YttrisL/maimai-dx-conversion-guide/docs/etape-1-pc-alls.md

# 🛠️ Étape 1 : Le Remplacement du PC Central (ALLS)

L'ancien PC *Ringedge 2* n'est pas assez puissant pour faire tourner *DX*. Vous avez besoin d'un PC **ALLS HX2**.
Alternativement, il est souvent plus simple (et moins cher) de trouver des PC **ALLS MX2**, et ceux-ci peuvent être modifiés (downgrade) pour correspondre exactement aux spécifications d'un HX2.

* **Stockage :** Le HX2 vient de base avec un SSD de 128 Go et un disque dur de 512 Go. Pour une installation sur serveur privé, ces disques suffisent.
* **Alimentation (Attention) :** L'alimentation interne du *Ringedge 2* fournissait directement les tensions nécessaires à différents composants de la borne *Finale*. Le connecteur molex en façade du *Ringedge 2* fournit au reste de la borne du 12v, du 5v et du 3,3v. Le nouveau PC *ALLS* ne possède pas ces connecteurs d'alimentation similaire. **La solution idéale** est d'ajouter une petite alimentation secondaire (arcade PSU) distincte de celle du PC *ALLS* pour alimenter les PCBs et les lumières. Une alimentation 12v/5v sera suffisante, aucun composant de la borne *Finale* n'exploite le 3,3v.

---

Passons à l'[Étape 2 : Affichage et dalles tactiles ADX](etape-2-affichage-tactile.md).
