YttrisL/maimai-dx-conversion-guide/docs/en/equipment-checklist.md

---
title: "☑️ Purchase checklist"
---

# ☑️ Purchase checklist

*Need details on where to buy, why, and alternatives? See the [full shopping list](equipment.md).*

## Mandatory hardware

- [ ] ALLS HX2
- [ ] Sega IO4 I/O board
- [ ] Aime reader (Gen. 3)
- [ ] **2x**{: .quantity-emphasis } HDX touchscreen
- [ ] **16x**{: .quantity-emphasis } HDX buttons
- [ ] **2x**{: .quantity-emphasis } OBSF-24TR button
- [ ] **1x**{: .quantity-emphasis } 4-port USB hub
- [ ] **1x**{: .quantity-emphasis } 5V/12V switching power supply

## Optional hardware (camera and QR-code)

- [ ] **1x**{: .quantity-emphasis } Player camera
- [ ] **2x**{: .quantity-emphasis } QR-code camera

## Small supplies

### Cables

- [ ] **1x**{: .quantity-emphasis } HDMI to DVI-D cable (3 m)
- [ ] **1x**{: .quantity-emphasis } DVI-D to DVI-D cable (2 m)
- [ ] **1x**{: .quantity-emphasis } DB-9 Female-Female cable
- [ ] **4x**{: .quantity-emphasis } DB-9 Male-Female cable (3 m)
- [ ] **1x**{: .quantity-emphasis } IEC C-13 cable (2 m)
- [ ] **2x**{: .quantity-emphasis } micro-USB cable
- [ ] **2x**{: .quantity-emphasis } 3.5 mm male-to-male jack cable

### Electronics

- [ ] **2x**{: .quantity-emphasis } TTL to RS-232 converter with female DB-9
- [ ] **2x**{: .quantity-emphasis } Raspberry Pi Pico
- [ ] **2x**{: .quantity-emphasis } Pico-2CH-RS232
- [ ] **2x**{: .quantity-emphasis } Headphone audio amplifier
- [ ] **2x**{: .quantity-emphasis } 3.5 mm female jack socket

### Hookup wire

- [ ] Flexible hookup wire (AWG 20), ideally in several colors

### Lighting (optional cameras)

- [ ] **1x**{: .quantity-emphasis } 12V warm white LED strip
- [ ] **1x**{: .quantity-emphasis } 12V common-anode RGB LED strip (about 20 cm)
- [ ] **1x**{: .quantity-emphasis } 12V red LED (with built-in resistor)

### Connectors

- [ ] **1x**{: .quantity-emphasis } Molex Mini-Fit Jr. 2x7-pin female connector
- [ ] **30x**{: .quantity-emphasis } Molex Mini-Fit Jr. female crimp pin
- [ ] **1x**{: .quantity-emphasis } JST-RA 2x10-pin female connector
- [ ] **30x**{: .quantity-emphasis } JST-RA female crimp pin
- [ ] **2x**{: .quantity-emphasis } JST-SM 8-pin female connector
- [ ] **2x**{: .quantity-emphasis } JST-SM 2-pin connector (male + female pair)
- [ ] JST-XH connector kit
- [ ] JST-PH connector kit

!!! abstract "Work in progress"
    More small supplies will be added to this checklist as they are detailed on the [full shopping list](equipment.md#small-supplies).
