YttrisL/maimai-dx-conversion-guide/docs/fr/equipment-checklist.md

---
title: "☑️ Checklist d'achat"
---

# ☑️ Checklist d'achat

*Besoin de détails sur où acheter, pourquoi, et des alternatives ? Consultez la [liste de courses complète](equipment.md).*

## Matériel obligatoire

- [ ] ALLS HX2
- [ ] Carte I/O Sega IO4
- [ ] Lecteur Aime (Gen. 3)
- [ ] **2x**{: .quantity-emphasis } Dalle tactile HDX
- [ ] **16x**{: .quantity-emphasis } Boutons HDX
- [ ] **2x**{: .quantity-emphasis } Bouton OBSF-24TR
- [ ] **1x**{: .quantity-emphasis } Hub USB 4 ports
- [ ] **1x**{: .quantity-emphasis } Alimentation à découpage 5V/12V

## Matériel optionnel (caméra et QR-code)

- [ ] **1x**{: .quantity-emphasis } Caméra des joueurs
- [ ] **2x**{: .quantity-emphasis } Caméra pour QR-Code

## Petites fournitures

### Câbles

- [ ] **1x**{: .quantity-emphasis } Câble HDMI vers DVI-D (3 m)
- [ ] **1x**{: .quantity-emphasis } Câble DVI-D vers DVI-D (2 m)
- [ ] **1x**{: .quantity-emphasis } Câble DB-9 Femelle-Femelle
- [ ] **4x**{: .quantity-emphasis } Câble DB-9 Mâle-Femelle (3 m)
- [ ] **1x**{: .quantity-emphasis } Câble IEC C-13 (2 m)
- [ ] **2x**{: .quantity-emphasis } Câble micro-USB
- [ ] **2x**{: .quantity-emphasis } Câble jack 3.5 mm mâle-mâle

### Électronique

- [ ] **2x**{: .quantity-emphasis } Convertisseur TTL vers RS-232 avec DB-9 femelle
- [ ] **2x**{: .quantity-emphasis } Raspberry Pi Pico
- [ ] **2x**{: .quantity-emphasis } Pico-2CH-RS232
- [ ] **2x**{: .quantity-emphasis } Ampli audio pour casque
- [ ] **2x**{: .quantity-emphasis } Prise jack 3.5 mm femelle

### Fils de câblage

- [ ] Fil de câblage souple (AWG 20), idéalement de plusieurs couleurs

### Éclairage (caméras optionnelles)

- [ ] **1x**{: .quantity-emphasis } Bande de LEDs blanc chaud 12V
- [ ] **1x**{: .quantity-emphasis } Bande de LEDs RGB 12V à anode commune (environ 20 cm)
- [ ] **1x**{: .quantity-emphasis } LED rouge 12V (avec résistance intégrée)

### Connecteurs

- [ ] **1x**{: .quantity-emphasis } Connecteur Molex Mini-Fit Jr. 2x7 broches femelle
- [ ] **30x**{: .quantity-emphasis } Broche Molex Mini-Fit Jr. femelle à sertir
- [ ] **1x**{: .quantity-emphasis } Connecteur JST-RA 2x10 broches femelle
- [ ] **30x**{: .quantity-emphasis } Broche JST-RA femelle à sertir
- [ ] **2x**{: .quantity-emphasis } Connecteur JST-SM 8 broches femelle
- [ ] **2x**{: .quantity-emphasis } Connecteur JST-SM 2 broches (paire mâle + femelle)
- [ ] Kit de connecteurs JST-XH
- [ ] Kit de connecteurs JST-PH

!!! abstract "En cours d'écriture"
    D'autres petites fournitures viendront s'ajouter à cette checklist au fur et à mesure qu'elles seront détaillées sur la [liste de courses complète](equipment.md#petites-fournitures).
