YttrisL/maimai-dx-conversion-guide/docs/fr/spiralglide-resources.md

---
title: "Les ressources de SpiralGlide"
---

# 🖨️ Les ressources de SpiralGlide

L'inspiration de base de ce guide est basé sur le travail de **SpiralGlide**, un membre de la communauté qui a documenté sa propre conversion *FiNALE → DX* et conçu plusieurs pièces imprimables en 3D pour l'opération. Cette page rassemble ces ressources d'origine.

## Les notes de conversion originales

* **[Notes de conversion DxNALE (PDF)](../resources/pdfs/dxnale-original-guide.pdf)** : le document de référence original rédigé par SpiralGlide, qui a servi de base à ce guide.

## Les pièces imprimables en 3D

SpiralGlide a modélisé les supports permettant de monter le lecteur Aime et le lecteur de QR code de DX de façon non-destructrice sur la tour centrale de la borne. Cela représente quatre fichiers `.stl`, répartis en deux ensembles.

### Support du lecteur Aime

Un seul bloc à imprimer, sur lequel s'installe le lecteur Aime de Star Horse 4 et qui vient prendre sa place dans la façade de la tour centrale dans les trous de vis prévus pour maintenir l'acrylique.

* **[maimai-aime-reader.stl](../resources/models/spiralglide/maimai-aime-reader.stl)** : support du lecteur Aime.
* **[maimai-aime-reader.ipt](../resources/models/spiralglide/maimai-aime-reader.ipt)** : fichier source Autodesk Inventor du support.

!!! lightbox
    Le support du lecteur Aime imprimé et monté dans la façade de la tour centrale, lecteur Aime en place. Photo par SpiralGlide

### Support du lecteur de QR code (DX Pass Reader)

Trois pièces qui s'empilent : le boîtier qui se loge dans la tour centrale, la plaque intermédiaire qui positionne la caméra (carte face arrière vers l'extérieur, code vers le bas), et la façade percée de deux ouvertures.

* **[dxnale-dx-pass-reader.stl](../resources/models/spiralglide/dxnale-dx-pass-reader.stl)** : boîtier principal.
* **[dxnale-dx-pass-reader-midpanel-v2.stl](../resources/models/spiralglide/dxnale-dx-pass-reader-midpanel-v2.stl)** : plaque intermédiaire.
* **[dxnale-dx-pass-reader-front-panel-v2.stl](../resources/models/spiralglide/dxnale-dx-pass-reader-front-panel-v2.stl)** : façade.

!!! lightbox
    Vue éclatée du support du lecteur de QR code : le boîtier, la plaque intermédiaire à deux ouvertures, et la façade « DX PASS READER »

---
