YttrisL/maimai-dx-conversion-guide/docs/etape-4-lecteur-aime.md

# 💳 Étape 4 : Le Lecteur de Cartes Aime

Les anciens lecteurs de cartes de la *Finale* sont obsolètes et ne fonctionneront pas avec *DX*.

1. Vous devez vous procurer un lecteur Aime moderne (Génération 3, numéro de pièce : **610-0955**).
2. Installez-le sur le panneau central de la borne, de préférence via une impression 3D pour réaliser une installation non-destructrice.
3. **Bonne nouvelle :** L'ordre des fils (pinout) sur le connecteur est presque identique à l'ancien modèle. Vous pouvez réutiliser les câbles de communication de l'ancien lecteur sans avoir à tout recâbler.
4. **Adresses et Branchement :**
   * Le lecteur Aime doit être branché au port **COM1**.
   * Le petit écran texte (VFD) doit être raccordé au port **COM2**.
   * Vous pouvez récupérer du courant 5V sur les anciens câbles pour alimenter ces deux éléments.

**Sur le PC *ALLS HX* :** Le port matériel correspondant au COM1 est la prise série située à gauche des ports USB et de la prise réseau. *([Manuel](pdfs/maimai-dx-manual-full.pdf), page 128)*.

---

Passons à l'[Étape 5 : Compatibilité avec le système d'origine via le Proxy](etape-5-proxy-compatibilite.md).
