YttrisL/maimai-dx-conversion-guide/docs/etape-6-son-casques.md

# 🎧 Étape 6 : Prises casques et Système Son

La borne *DX* propose des prises casques pour les joueurs, ce qui n'existait pas sur *Finale*.

L'ordinateur *ALLS HX* possède 4 sorties audio classiques (type Jack). Trois sont situées sur la carte mère principale, et une sur une carte d'extension *([Manuel](pdfs/maimai-dx-manual-full.pdf), page 128)*.
**Attention :** L'ordinateur ne sort qu'un son "pré-amplifié" (très faible). Dans une vraie borne *DX*, ce son passe par un gros amplificateur dédié. Vous pouvez réutiliser l'amplificateur de la *Finale* pour les haut-parleurs principaux, mais il ne gérera pas les nouvelles prises casques.

Voici à quoi correspondent les ports audio de l'ordinateur : *(Voir [manuel](pdfs/maimai-dx-manual-full.pdf), page 193)*

* **FRONT :** Sortie pour les haut-parleurs du Joueur 1
* **REAR :** Sortie pour les haut-parleurs du Joueur 2
* **C/W :** Sortie pour la prise casque du Joueur 1
* **SIDE :** Sortie pour la prise casque du Joueur 2

## Comment installer les prises casques

Puisque le signal pour les casques (sorties C/W et SIDE) est trop faible, vous devez acheter un ou deux petits amplificateurs audio bon marché. **Inutile d'acheter des amplis avec des molettes de volume :** le volume des casques se règle numériquement directement dans les menus du jeu *DX*.

Pour l'installation physique des prises (qui sont de simples connecteurs Jack 3.5mm femelles), vous avez deux options :

1. **La méthode fidèle :** Percer la coque en plastique sous les boutons (comme sur une vraie *DX*) pour y encastrer les prises.
2. **La méthode non-destructrice :** Installer les deux prises casque au centre de la borne, entre les deux joueurs, via un boîtier réalisé manuellement.

**Astuce :** En salle d'arcade, les prises jack s'abîment très vite à force de brancher/débrancher les écouteurs. Prévoyez un système où la prise fixée sur la coque est facilement remplaçable (par exemple, reliez-la à l'amplificateur interne avec un câble détachable, plutôt que de souder le connecteur directement sur l'ampli).

---

Étape suivante (optionnelle) : les [Lumières](etape-7-lumieres.md).
