YttrisL/maimai-dx-conversion-guide/docs/lexique.md

# 📖 Petit Lexique pour les Débutants

Pour ne pas être perdu dans les termes techniques :

* **ALLS (MX2 / HX2) :** C'est le nom de l'ordinateur standard utilisé par Sega pour faire tourner les jeux récents. Il remplace l'ancien PC de Finale (nommé Ringedge 2).
* **Carte I/O (Input/Output) :** C'est la carte électronique qui fait le lien entre le PC et la borne. Elle capte l'appui sur les boutons. Dans le cas de *maimai Finale*, il s'agit d'une **Sega IO3**. Pour *DX*, elle doit être remplacée par une **Sega IO4**.
* **Ports COM (COM1, COM3...) :** Ce sont les "adresses" (ou canaux) virtuelles par lesquelles le PC communique avec certains périphériques spécifiques (comme les dalles tactiles ou le lecteur de carte *Aime*). Aujourd'hui, la plupart des connexions sur Port COM se font via des ports virtuels, toutefois un ALLS HX2 dispose de quatre connexions physiques pour y connecter le matériel de la borne.
* **Aime / VFD :** Le lecteur de cartes sans contact (NFC) utilisé par les joueurs pour sauvegarder leur profil. Le *VFD* (Vacuum Fluorescent Display) est le petit écran à affichage rétro (souvent vert ou bleu) qui affiche le solde d'argent ou d'autres informations textuelles.

---

Le vocabulaire est clair ? Passons à la [Liste de courses](materiel.md).
