YttrisL/maimai-dx-conversion-guide/docs/materiel.md

# 🛒 Liste de courses : Le matériel nécessaire

Avant de commencer, voici la liste des composants à acquérir pour réaliser cette conversion :

## Matériel Obligatoire

* Un PC ALLS HX2 (ou un MX2 modifié).
* Une carte I/O Sega IO4.
* Deux dalles tactiles ADX.
* Un lecteur Aime de 3ème génération (référence de la pièce : 610-0955).
* Un câble DisplayPort (ou DisplayPort vers DVI) et un câble DVI-D pour les écrans.
* Deux petits amplificateurs audio pour gérer les prises casques.

## Pour le Proxy ("Traduction" des données)

* Deux Raspberry Pi 5 avec leur bloc d'alimentation.
* Deux adaptateurs "USB-to-Serial" avec puces FTDI (prévoyez-en 6 si vous gérez le tactile **et** les LEDs via proxy).
* Deux adaptateurs "Null Modem" pour faire correspondre les fiches mâle-femelle des adaptateurs "USB-to-Serial" à la connectique du ALLS.

## Matériel Optionnel (Son, Caméras, Finitions)

* Une webcam classique et bon marché pour la caméra du joueur.
* Deux webcams au format strict UVC 640x480 pour les lecteurs de QR-Code.
* Un Hub USB (de préférence avec sa propre alimentation).

---

Consultez ensuite les [avertissements](avertissements.md) avant de vous lancer.
