YttrisL/maimai-dx-conversion-guide/docs/en/warnings.md

---
title: "⚠️ Warnings"
---

# ⚠️ Warnings and Considerations

Before you dive in, here is the reality of the project:

* **It is practically irreversible.** We avoid destructive modifications as much as possible, but most of the FiNALE cabinet's core components will be replaced with DX-compatible hardware. Going back to *FiNALE* remains possible in theory if you keep all the original parts, but it would be a fresh conversion, just as tedious.
* **It is expensive.** Budget **around 2000 to 2500 EUR** for the parts. Most of the hardware is only available second-hand, on Japanese resale sites or from private sellers who set their own prices. The total therefore varies with the period and availability.
* **It takes time.** Do not expect to start in the morning and be done by the evening. Even with every part and tool on hand, plan for **several days** of work. *If you are an operator*, keep in mind that the cabinet will be out of service until the conversion is complete.
* **Test beforehand.** Make sure your *FiNALE* cabinet works perfectly before you start, since several of its components will be reused. **Fix any power, sound, LED or screen problem first.** The buttons, touchscreens, Aime readers, camera, I/O board and RingEdge 2, on the other hand, will be replaced: a fault on one of them is therefore minor.

The task is complex, but this guide presents every point in a simple and detailed way, explaining the concepts you need at each step.

Also keep in mind that, even though the goal is the most faithful DX experience possible, **this cabinet will remain a conversion**. Gameplay does not suffer from it, but some details specific to a real DX can never be reproduced on a FiNALE base.

!!! tip "Before you dive in"
    Most components will come from Asia, often with long delivery times. To avoid an out-of-service cabinet for several months, **get every component before starting the conversion**, and **check that they work**. The next page details the purchases to plan.

If, knowing these warnings, you are still determined to go ahead, let's move on to the rest of the guide.

---

Not a technical expert? Feel free to consult the [glossary](glossary.md) before moving on to the [shopping list](equipment.md).
