YttrisL/maimai-dx-conversion-guide/docs/fr/index.md

---
title: "Accueil"
---

# Guide Complet : Projet "DxNALE"

## Convertir une borne FiNALE en DX

Bienvenue dans ce guide détaillé pour **convertir une borne d'arcade FiNALE en DX**. Il s'appuie sur [les ressources de SpiralGlide](spiralglide-resources.md), enrichies pour rester accessibles *même si vous n'êtes pas ingénieur en électronique*.

---

## Qu'est-ce que "DxNALE" ?

DxNALE est le nom donné par la communauté aux bornes FiNALE converties pour faire tourner DX. Les deux systèmes sont radicalement différents : **DX ne peut pas tourner sur une borne FiNALE d'origine.**

Une rumeur tenace veut que la conversion soit un travail titanesque, presque irréalisable. **Il n'en est rien.** Certaines étapes sont effectivement complexes, mais ce guide vous accompagne tout au long de l'opération.

!!! tip "L'objectif : une fidélité logicielle parfaite"
    Il serait possible de modifier les données du jeu pour le rendre compatible avec n'importe quelle modification matérielle. Ce guide vise au contraire une fidélité logicielle totale.

    **Aucune modification logicielle du jeu n'est tolérée.** Le jeu doit "penser" qu'il tourne sur une borne d'origine : toute notre adaptation matérielle doit donc lui être invisible.

    Avantage : la borne obtenue est en théorie compatible avec la philosophie de la plupart des grands serveurs privés pour DX.

---

## Par où commencer ?

1. Lisez les **[Avertissements](warnings.md)** pour comprendre les enjeux et les conséquences de la conversion.
2. Consultez la **[Liste de courses](equipment.md)** : vous aurez besoin de chacun des éléments mentionnés.
3. Suivez les **étapes dans l'ordre**, en commençant par l'[Étape 1 : PC Central (ALLS)](step-1-alls-and-psu.md).

Un terme vous semble obscur ? Le [Lexique](glossary.md) regroupe toutes les définitions utiles aux débutants.

Les protocoles série sont au cœur de cette conversion. Si vous ne les maîtrisez pas, l'annexe "[Comprendre les protocoles série](understanding-serial-protocols.md)" les explique en partant de zéro.

**Félicitations d'avance !** En suivant toutes ces étapes, vous obtiendrez une borne *DxNALE* 100 % fonctionnelle et prête pour le jeu en ligne.

---

Prêt à vous lancer ? Commençons par les [Avertissements](warnings.md).
