YttrisL/maimai-dx-conversion-guide/docs/fr/secondhand-market.md

---
title: "Le marché de l'occasion"
---

# 📦 À propos du marché de l'occasion japonais

## Introduction

*Hormis les petites fournitures*, la plupart des composants de cette conversion **ne se trouvent pas dans le commerce**. C'est du matériel d'arcade très spécifique, vendu uniquement par les fabricants officiels, et passer par le service après-vente de Sega est évidemment impossible. Il ne reste donc que la vente entre particuliers.

**Nous dépendons donc de ce qui est disponible sur le marché de l'occasion.** Une carte Sega IO4 ou un lecteur Aime se trouvent assez facilement, un ALLS HX2 beaucoup moins, et une dalle tactile officielle de DX est pour ainsi dire introuvable. Pour certaines pièces, des alternatives existent. Pour les autres, il faudra prendre votre mal en patience et guetter une offre sur le marché de l'occasion japonais.

!!! tip "D'où viennent les pièces détachées ?"
    La plupart des pièces d'occasion japonaises proviennent de bornes démantelées pour être revendues plus facilement, le plus souvent après la fermeture d'une salle d'arcade ou parce que la borne n'attirait plus de joueurs. DX étant très populaire, ses bornes sont rarement exportées, et encore plus rarement démontées pour être vendues en pièces détachées.

    Heureusement, **la plupart des composants Sega sont interchangeables** et réutilisés d'une borne à l'autre, y compris sur des machines bien moins populaires que DX, dont on trouve beaucoup plus facilement les pièces.

## Acheter via un proxy

La plupart des pièces de la [liste de courses](equipment.md) se trouvent sur **JDirectItems Auction**, le plus grand site d'enchères du Japon. Problème : comme la grande majorité des sites de vente japonais, il exige **une adresse, un numéro de téléphone et un moyen de paiement japonais**. Sans résider au Japon, impossible donc d'y acheter directement.

C'est là qu'interviennent les **services de proxy d'achat** : des entreprises disposant d'une adresse et d'un compte au Japon, qui enchérissent, achètent et réceptionnent les colis en votre nom, puis vous les réexpédient à l'international. Ils facturent une commission et des frais de service, en plus du prix de l'article et des frais d'envoi.

Parmi ces services :

* **[Neokyo]({{NEOKYO}})**
* **[Zenmarket]({{ZENMARKET}})**
* **[FROM JAPAN]({{FROM_JAPAN}})**
* **[Buyee]({{BUYEE}})** : l'un des plus connus et des plus anciens, mais lisez l'avertissement ci-dessous.

!!! warning "Buyee n'expédie pas certaines pièces électroniques"
    Buyee refuse d'expédier à l'international tout article contenant une pile ou une batterie au lithium, en application des réglementations sur le transport aérien de matières dangereuses. Or, certaines pièces recherchées, comme le ALLS HX2, embarquent une petite pile bouton au lithium qui alimente leur horloge interne (RTC) hors tension. **Dans les faits, ces pièces ne peuvent donc pas être expédiées via Buyee.**

    Pour ces articles, préférez un service comme Neokyo ou Zenmarket, qui n'appliquent pas cette restriction.

Le fonctionnement est similaire d'un service à l'autre :

1. Vous créez un compte.
2. Vous soumettez le lien de l'article qui vous intéresse (ou parcourez JDirectItems Auction directement depuis leur site).
3. Vous créditez votre compte du montant nécessaire, et le proxy se charge de l'achat.
4. Le proxy reçoit l'article et le stocke pour vous.
    * La plupart des services stockent gratuitement les articles pendant une certaine durée.
    * Vous pouvez ainsi **regrouper plusieurs articles** dans leur entrepôt pour tout expédier en un seul colis.
5. Une fois prêt, demandez le conditionnement : le proxy emballe vos articles et les expédie à votre adresse hors du Japon.

!!! tip "Demandez des photos avant l'envoi"
    Une fois l'article arrivé dans leur entrepôt, vous pouvez généralement demander **des photos supplémentaires** avant de valider l'envoi. C'est très utile pour vérifier l'état d'une pièce d'occasion avant qu'elle ne traverse la moitié du globe. Vous ne serez pas remboursé en cas de problème, mais vous saurez tout de suite s'il faut chercher la pièce ailleurs, sans attendre de recevoir le colis.

## Astuces pour la recherche

Trouver la bonne pièce sur JDirectItems Auction peut être frustrant sans quelques bases :

* **Cherchez avec les références officielles.** Une recherche en anglais ou en français ne donne presque jamais de résultats pertinents. Utilisez plutôt les noms et références des schémas et manuels officiels (par exemple `ALLS HX2`, `IO4`, `Aime`), qui restent les mêmes en japonais puisqu'il s'agit de références commerciales. Un traducteur (DeepL, Google Traduction) vous aidera à comprendre le titre et la description d'une annonce.
* **Ne fuyez pas la mention « ジャンク » (*junk*).** Du matériel fonctionnel est souvent vendu ainsi, simplement parce qu'il n'a pas été testé récemment. Ce n'est pas forcément cassé : c'est juste vendu « en l'état », sans garantie.
* **Vérifiez le vendeur.** Le pourcentage d'évaluations positives (en haut à droite de l'annonce) est un bon indicateur de fiabilité. Un vendeur professionnel habitué à démonter des bornes d'arcade est généralement un gage de sérieux.
* **Examinez les photos.** Les vendeurs japonais sont généralement très rigoureux sur les photos, même sans description en anglais. Zoomez sur les connecteurs, l'état des broches et les étiquettes ou marquages qui confirment la référence exacte de la pièce.
* **Surveillez l'heure de fin d'enchère.** Les enchères se terminent à l'heure japonaise (JST, UTC+9), souvent en pleine nuit en France. La plupart des proxys permettent de placer à l'avance une **enchère automatique maximale** : inutile de rester éveillé pour surenchérir à la dernière seconde.
* **Anticipez les frais annexes.** Le prix affiché n'est jamais le prix final. Ajoutez :
    * la commission du proxy ;
    * le transport jusqu'à son entrepôt ;
    * l'envoi international, souvent calculé au poids **et** au volume ;
    * les éventuels frais de douane à la réception, qui varient selon votre pays.

    Une carte électronique compacte reste généralement raisonnable à expédier, mais gardez ce calcul en tête avant d'enchérir trop haut sur une pièce rare.
* **Créez une alerte.** La plupart des proxys permettent d'enregistrer une recherche et d'être notifié dès qu'un nouvel article correspondant apparaît. C'est particulièrement utile pour les pièces rares comme le ALLS HX2, qui peuvent mettre des semaines, voire des mois, à réapparaître.
