YttrisL/maimai-dx-conversion-guide/docs/fr/warnings.md

---
title: "⚠️ Avertissements"
---

# ⚠️ Avertissements et Considérations

Avant de vous lancer, voici la réalité du projet :

* **C'est pratiquement irréversible.** Nous évitons autant que possible les modifications destructives, mais la plupart des éléments centraux de la borne FiNALE vont être remplacés par du matériel compatible DX. Revenir à *FiNALE* reste théoriquement possible si vous conservez toutes les pièces d'origine, mais ce serait une nouvelle conversion, tout aussi fastidieuse.
* **C'est coûteux.** Comptez **environ 2000 à 2500 €** de pièces. La plupart du matériel ne se trouve que d'occasion, sur les sites de revente japonais ou auprès de particuliers qui fixent librement leurs prix. Ce montant varie donc selon la période et la disponibilité.
* **C'est long.** N'espérez pas commencer le matin et terminer le soir. Même avec toutes les pièces et tout le matériel en main, comptez **plusieurs jours** de travail. *Si vous êtes exploitant*, gardez en tête que la borne restera hors service jusqu'à la fin de la conversion.
* **Testez avant.** Vérifiez que votre borne *FiNALE* fonctionne parfaitement avant de commencer, car plusieurs de ses composants seront réutilisés. **Réglez d'abord tout problème d'alimentation, de son, de LEDs ou d'écrans.** À l'inverse, les boutons, les dalles tactiles, les lecteurs Aime, la caméra, la carte I/O et le RingEdge 2 seront remplacés : un défaut sur l'un d'eux est donc mineur.

La tâche est complexe, mais ce guide présente chaque point de façon simple et détaillée, en expliquant à chaque étape les notions nécessaires.

Gardez aussi en tête que, même si l'objectif est une expérience DX la plus fidèle possible, **cette borne restera une conversion**. L'expérience de jeu n'en souffre pas, mais certains détails propres à une véritable DX ne pourront jamais être reproduits sur une base FiNALE.

!!! tip "Avant de vous lancer"
    La plupart des composants viendront d'Asie, avec des délais de livraison souvent longs. Pour éviter une borne hors service pendant plusieurs mois, **procurez-vous tous les composants avant de commencer la conversion**, et **vérifiez qu'ils fonctionnent**. La page suivante détaille les achats à prévoir.

Si, en connaissance de ces avertissements, vous êtes toujours décidé à vous lancer, passons à la suite du guide.

---

Vous n'êtes pas un expert technique ? N'hésitez pas à consulter le [lexique](glossary.md) avant de passer à la [liste de courses](equipment.md).
