YttrisL/maimai-dx-conversion-guide/docs/fr/conclusion.md

---
title: "Conclusion"
---

# 🎉 Conclusion

**Félicitations !** Si vous avez suivi toutes ces étapes, vous possédez désormais une borne *maimai DxNALE* fonctionnelle et prête pour le jeu en ligne !

---

## Pour aller plus loin

Le guide est terminé, mais quelques annexes restent à portée de main si besoin :

* **[Manuels officiels](official-manuals.md)** - Les manuels de maintenance d'origine (*maimai DX* et *maimai PiNK*), pour retrouver une référence précise ou une procédure constructeur.
* **[Schémas de câblage](wiring-diagrams.md)** - Les planches de câblage extraites de ces manuels en haute résolution, pour retrouver un fil sans avoir à zoomer dans un PDF de plusieurs dizaines de Mo.
* **[Comprendre les protocoles série](understanding-serial-protocols.md)** - Un petit cours pour ceux qui découvrent l'UART, le RS-232, le RS-485, le JVS ou l'USB-CDC, et veulent comprendre comment ces appareils "se parlent".
* **[Lexique](glossary.md)** - Un rappel des termes techniques employés tout au long du guide, si un mot vous échappe encore.
* **[Liens utiles](useful-links.md)** - Des ressources externes qui ne concernent pas directement la conversion, mais dont le contenu peut s'avérer utile.

---
