YttrisL/maimai-dx-conversion-guide/docs/fr/useful-links.md

---
title: "Liens utiles"
---

# 🔗 Liens utiles

Cette page recense des ressources externes qui ne concernent pas directement la conversion *FiNALE → DX*, mais dont le contenu peut néanmoins s'avérer utile.

* **[Guide d'achat de l'ADX Controller (Yuancon)]({{ADX_CONTROLLER_PURCHASING_GUIDE}})** : le guide d'achat de Yuancon pour son ADX Controller. Bien qu'il ne nous concerne pas directement, les derniers chapitres de son contenu reste utile pour les différents modèles de boutons disponibles ainsi que leur maintenance.
* **[Guide pour imager un SSD ALLS (redive.world)]({{REDIVE_WORLD_ALLS_IMAGING_GUIDE}})** : bien que ce guide soit destiné à *Wacca* et non à *maimai DX*, il reste utile, notamment pour sa méthode permettant d'imager le SSD d'un ALLS sans déclencher ses protections. Ses autres pages contiennent également des informations et photos intéressantes sur le fonctionnement de certaines PCB standards de Sega, comme l'IO4.
* **[Références et spécifications des ALLS (arcade-docs)]({{ARCADE_DOCS_ALLS_REFERENCES}})** : reprend les références de plusieurs ALLS ainsi que leurs spécifications techniques.
* **[Documentation officielle HanDevice]({{HANDEVICE_OFFICIAL_DOCUMENTATION}})** : la documentation officielle de HanDevice, le fabricant de la dalle tactile HDX. Elle est en chinois, mais reste consultable via le traducteur intégré du navigateur, et propose entre autres une page dédiée à l'installation de sa dalle tactile dans une borne *maimai FiNALE*.

---
