YttrisL/maimai-dx-conversion-guide/docs/fr/step-2-touchscreen-display.md

---
title: "📺 2 - Écrans et dalles tactiles"
---

# 📺 Étape 2 : L'Affichage et les Dalles Tactiles HDX

--8<-- "includes/wip-fr.md"

Commençons par installer l'affichage et les dalles tactiles.

## Les connexions vidéo

Le jeu est programmé pour envoyer la vidéo d'une manière bien précise aux deux écrans. L'ordre doit être respecté. *(Référence : [Manuel](../resources/pdfs/maimai-dx-instruction-manual-full.pdf) officiel de la borne DX, page 128)*

* **Joueur 1 (P1) :** Peut être branché sur le port **HDMI** ou **DisplayPort** (Le [manuel officiel](../resources/pdfs/maimai-dx-instruction-manual-full.pdf) recommande HDMI).
* **Joueur 2 (P2) :** Doit être branché sur le port **DVI**.

Il existe toutefois une légère différence native entre les écrans d'une *FiNALE* et d'une *DX*. Dans les deux cas, il s'agit d'écrans 1920x1080 cadencés à 60 Hz, mais les écrans de *FiNALE* mesurent 42" de diagonale, alors que les écrans de *DX* mesurent 43". La différence est pratiquement imperceptible en jeu.

## Les dalles tactiles HDX

Retirez les anciennes dalles tactiles de la borne *FiNALE* (maintenues par 8 vis) et installez les nouvelles dalles HDX.
Il faut ensuite raccorder les dalles aux bonnes "adresses" (Ports COM) sur le ALLS, sinon le jeu confondra les deux joueurs : *([Manuel](../resources/pdfs/maimai-dx-instruction-manual-full.pdf), page 128)*

* **Joueur 1 :** Doit être branché au Port **COM3**.
* **Joueur 2 :** Doit être branché au Port **COM4**.

!!! lightbox
    Vue arrière d'un ALLS HX2 : des flèches rouges désignent les ports DB9 des dalles tactiles sur la carte d'extension, P1 en bas à droite et P2 en haut à gauche

Contrairement à d'autres kits de conversion, la carte I/O HanDevice fournie avec les dalles HDX expose directement un port série UART. Vous pouvez donc la raccorder directement au ALLS, sans transformation de signal ni Raspberry Pi intermédiaire - voir la [Liste de courses](equipment.md) pour le détail de cette carte I/O.

---

Passons à l'[Étape 3 : Le Lecteur de Cartes Aime](step-3-aime-reader.md).
