YttrisL/maimai-dx-conversion-guide/docs/fr/step-5-audio-headphones.md

---
title: "🎧 5 - Prises casques et son"
---

# 🎧 Étape 5 : Prises casques et système son

Contrairement à FiNALE qui n'en possédait pas, DX apporte nativement aux joueurs une **prise casque avec contrôle du volume en jeu**. Son installation est très simple.

## Branchement des haut-parleurs

Le système son existant de la borne se raccorde sans aucune modification : il suffit de brancher la prise jack sur le port approprié de la carte mère, comme expliqué à [l'étape 1](step-1-alls-and-psu.md).

- **FRONT** : côté Joueur 1
- **REAR** : côté Joueur 2

!!! lightbox
    Vue arrière d'un ALLS HX2 : la carte mère et la carte d'extension avec leurs connecteurs, les flèches rouges P1 et P2 désignent les sorties haut-parleurs

## Les prises casques

Le ALLS dispose de 4 prises jack audio : trois à l'emplacement classique et une quatrième sur la carte d'extension. Les sorties casques utilisent les deux ports restants :

- **C/W** : prise casque du Joueur 1
- **SIDE** : prise casque du Joueur 2

!!! lightbox
    Vue arrière d'un ALLS HX2 : des flèches rouges désignent les sorties casques, C/W pour P1 sur la carte mère et SIDE pour P2 sur la carte d'extension

!!! warning
    Le ALLS ne sort qu'un son **pré-amplifié (très faible)**. Dans une vraie borne *DX*, ce son passe par un gros amplificateur dédié. Une borne FiNALE n'en possède aucun pour les casques, puisqu'elle n'avait pas de prise casque d'origine : ces sorties ne sont donc pas utilisables telles quelles.

### Installation d'un ampli

Le signal des sorties C/W et SIDE étant trop faible, il faut acheter **un ou deux petits amplificateurs audio bon marché**, un par joueur, ainsi que des câbles jack 3.5 mm mâle-mâle pour les relier au ALLS. Tout est référencé dans la [liste de courses](equipment.md#electronique).

!!! tip "Inutile d'acheter des amplis avec des molettes de volume"
    Sur DX, le volume des casques se règle numériquement dans les menus du jeu. Toutefois, si votre FiNALE avait déjà été modifiée avec une prise casque, vous pouvez réutiliser l'ampli en place.

### Mise en place sur la borne

Les prises sont de simples connecteurs Jack 3.5 mm femelles. Deux options s'offrent à vous pour les installer :

1. **La méthode fidèle :** percer la coque en plastique sous les boutons (comme sur une vraie DX) pour y encastrer les prises.
2. **La méthode non destructrice :** installer les deux prises au centre de la borne, entre les deux joueurs, dans un boîtier réalisé manuellement.

!!! tip "Durabilité des prises jack"
    En salle d'arcade, les prises jack s'abîment vite à force de brancher et débrancher les écouteurs. Prévoyez une prise fixée sur la coque **facilement remplaçable** : reliez-la à l'amplificateur avec un câble détachable plutôt que de souder le connecteur directement sur l'ampli.

## En résumé
!!! tldr "Les grandes lignes"
    Pour le son et les casques :

    * Brancher les haut-parleurs existants sur les sorties FRONT et REAR du ALLS.
    * Relier les sorties C/W (Joueur 1) et SIDE (Joueur 2) à un ampli audio chacun, avec des câbles jack 3.5 mm mâle-mâle.
    * Raccorder chaque ampli à une prise jack 3.5 mm femelle pour le casque.
    * Installer les prises sur la coque sous les boutons, ou dans un boîtier central entre les joueurs.

---

Passons à l'[Étape 6 : Lumières](step-6-lighting.md).
