YttrisL/maimai-dx-conversion-guide/docs/fr/official-manuals.md

---
title: "Manuels officiels"
---

# 📚 Manuels officiels

Cette page recense les manuels officiels référencés tout au long de ce guide.

* [Instruction Manual maimai DX](../resources/pdfs/maimai-dx-instruction-manual-full.pdf) : il s'agit du manuel officiel de maintenance de la borne dans sa version **maimai DX**, celle vers laquelle ce guide propose la conversion.
* [Service Manual maimai DX](../resources/pdfs/maimai-dx-service-manual-full.pdf) : le *service manual* officiel de **maimai DX**, centré sur le logiciel de la borne plutôt que sur le matériel.
* [Service Manual ALLS HX2](../resources/pdfs/alls-hx2-service-manual-full.pdf) : le *service manual* officiel du PC **ALLS HX2**, le PC central utilisé par *maimai DX* (voir l'étape [ALLS et PSU](step-1-alls-and-psu.md)).
* [Manuel maimai PiNK](../resources/pdfs/maimai-pink-manual-full.pdf) : il s'agit du manuel officiel de maintenance de la borne dans sa version **maimai PiNK**, une révision antérieure à *FiNALE*. Toutefois, il n'y a aucune différence notable d'un point de vue matériel entre PiNK et FiNALE.

Les manuels *maimai DX* et *maimai PiNK* contiennent chacun, dans leurs dernières pages, un schéma de câblage complet de la borne. Une extraction haute résolution de ces planches, plus rapide à consulter que les PDF complets, est disponible sur la page [Schémas de câblage](wiring-diagrams.md).

---
