YttrisL/maimai-dx-conversion-guide/docs/resources/images/step-1-alls-and-psu/alls-hx2-rear-connectors.jpg

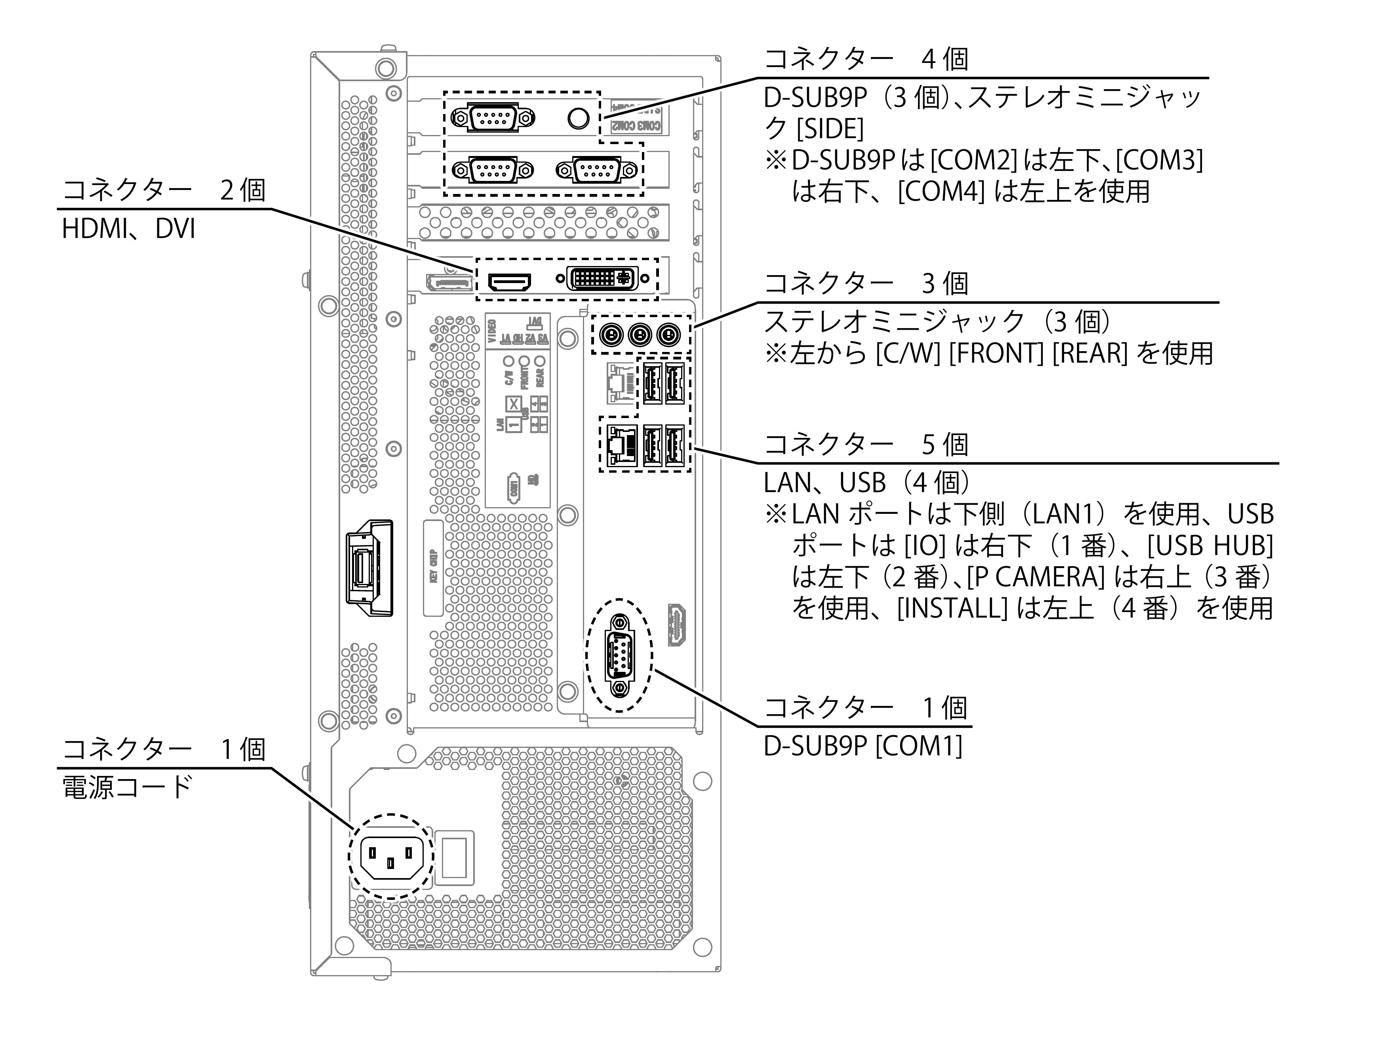
docs/resources/images/step-1-alls-and-psu/alls-hx2-rear-connectors.jpg
